Fbeen/RetroLink/src/USBHost.c

#include <string.h>
#include "CH559.h"
#include "USBHost.h"
#include "hid_mouse.h"
#include "config.h"
#include "console.h"
#include "led.h"

/* laatste HID report voor wizard */
uint8_t __xdata g_last_report[LEARN_MAX_REPORT];
uint8_t g_last_report_len = 0;

/* Your parsers live elsewhere; keep the same signature you used before */
extern void parseMouseData(uint8_t hub, vendor_product_id_t *vp, unsigned char __xdata *report);
extern void parseJoystickData(uint8_t *report);
extern void rm_init(void);
extern void rj_init(void);

/* remember if there is a USB device connected */
static uint8_t device_present = 0;
static controller_mode_t currentMode = CTRL_MODE_NONE;

/* ---------------- Setup requests ---------------- */

typedef const unsigned char __code *PUINT8C;

__code unsigned char GetDeviceDescriptorRequest[] =
{
    USB_REQ_TYP_IN, USB_GET_DESCRIPTOR,
    0x00, USB_DESCR_TYP_DEVICE,
    0x00, 0x00,
    sizeof(USB_DEV_DESCR), 0x00
};

__code unsigned char GetConfigurationDescriptorRequest[] =
{
    USB_REQ_TYP_IN, USB_GET_DESCRIPTOR,
    0x00, USB_DESCR_TYP_CONFIG,
    0x00, 0x00,
    /* first fetch only config header size */
    sizeof(USB_CFG_DESCR), 0x00
};

__code unsigned char SetUSBAddressRequest[] =
{
    USB_REQ_TYP_OUT, USB_SET_ADDRESS,
    USB_DEVICE_ADDR, 0x00,
    0x00, 0x00,
    0x00, 0x00
};

__code unsigned char SetupSetUsbConfig[] =
{
    USB_REQ_TYP_OUT, USB_SET_CONFIGURATION,
    0x00, 0x00,
    0x00, 0x00,
    0x00, 0x00
};

__code unsigned char SetHIDIdleRequest[] =
{
    USB_REQ_TYP_CLASS | USB_REQ_RECIP_INTERF, HID_SET_IDLE,
    0x00, 0x00,
    0x00, 0x00,
    0x00, 0x00
};

/* ---------------- Buffers ---------------- */

#ifndef MAX_PACKET_SIZE
#define MAX_PACKET_SIZE 64
#endif

__at(0x0000) unsigned char __xdata RxBuffer[MAX_PACKET_SIZE];
__at(0x0100) unsigned char __xdata TxBuffer[MAX_PACKET_SIZE];

#define RECEIVE_BUFFER_LEN 128
__xdata unsigned char receiveDataBuffer[RECEIVE_BUFFER_LEN];

/* ---------------- Minimal state ---------------- */

uint8_t endpoint0Size;

static root_hub_device_t __xdata rootHubDevice;
static hid_device_t __xdata hidDevice;
static vendor_product_id_t __xdata vendorProductID;

/* ---------------- Helpers ---------------- */

/*
 * Copy a setup/request packet from code memory to the TX buffer.
 */
static void fillTxBuffer(PUINT8C data, unsigned char len)
{
    unsigned char i;
    for (i = 0; i < len; i++)
        TxBuffer[i] = data[i];
}

/*
 * Set the current USB device address for host communication.
 */
static void setHostUsbAddr(unsigned char addr)
{
    USB_DEV_AD = (USB_DEV_AD & bUDA_GP_BIT) | (addr & 0x7F);
}

/*
 * Configure USB speed (full-speed or low-speed).
 */
static void setUsbSpeed(unsigned char fullSpeed)
{
    if (fullSpeed)
    {
        USB_CTRL &= ~bUC_LOW_SPEED;
        UH_SETUP &= ~bUH_PRE_PID_EN;
    }
    else
    {
        USB_CTRL |= bUC_LOW_SPEED;
    }
}

/*
 * Disable the root hub port and reset internal state.
 */
static void disableRootHubPort(void)
{
    rootHubDevice.status  = ROOT_DEVICE_DISCONNECT;
    rootHubDevice.address = 0;
    rootHubDevice.speed   = 1;

    UHUB0_CTRL = 0;
}

/*
 * Reset the root hub port and prepare for enumeration.
 */
static void resetRootHubPort(void)
{
    endpoint0Size = DEFAULT_ENDP0_SIZE;
    setHostUsbAddr(0);
    setUsbSpeed(1);

    UHUB0_CTRL = (UHUB0_CTRL & ~bUH_LOW_SPEED) | bUH_BUS_RESET;
    delay(15);
    UHUB0_CTRL = (UHUB0_CTRL & ~bUH_BUS_RESET);

    delayUs(250);
    UIF_DETECT = 0;
}

/*
 * Enable the root hub port if a device is attached.
 * Detects device speed and configures the controller accordingly.
 */
static unsigned char enableRootHubPort(void)
{
    if (USB_HUB_ST & bUHS_H0_ATTACH)
    {
        if ((UHUB0_CTRL & bUH_PORT_EN) == 0x00)
        {
            if (USB_HUB_ST & bUHS_DM_LEVEL)
            {
                rootHubDevice.speed = 0;
                UHUB0_CTRL |= bUH_LOW_SPEED;
            }
            else
            {
                rootHubDevice.speed = 1;
                UHUB0_CTRL &= ~bUH_LOW_SPEED;
            }
        }
        UHUB0_CTRL |= bUH_PORT_EN;
        return ERR_SUCCESS;
    }
    return ERR_USB_DISCON;
}

/*
 * Select the currently active USB device (address + speed).
 */
static void selectHubPort(void)
{
    setHostUsbAddr(rootHubDevice.address);
    setUsbSpeed(rootHubDevice.speed);
}

/* ---------------- USB transfers ---------------- */

/*
 * Perform a low-level USB host transfer (SETUP/IN/OUT).
 * Handles retries, NAKs and toggle bits.
 */
static unsigned char hostTransfer(unsigned char endp_pid, unsigned char tog, unsigned short timeout)
{
    static unsigned short retries = 0;
    static unsigned char  r;
    static unsigned short i;

    UH_RX_CTRL = tog;
    UH_TX_CTRL = tog;

    do
    {
        UH_EP_PID = endp_pid;
        UIF_TRANSFER = 0;

        for (i = 200; i != 0 && UIF_TRANSFER == 0; i--)
            delayUs(1);

        UH_EP_PID = 0x00;

        if (UIF_TRANSFER == 0)
            return ERR_USB_UNKNOWN;

        if (U_TOG_OK)
            return ERR_SUCCESS;

        r = USB_INT_ST & MASK_UIS_H_RES;

        if (r == USB_PID_STALL)
            return (r | ERR_USB_TRANSFER);

        if (r == USB_PID_NAK)
        {
            if (timeout == 0)
                return (r | ERR_USB_TRANSFER);
            if (timeout < 0xFFFF)
                timeout--;
            /* keep retrying */
        }
        else
        {
            /* For most cases, treat other responses as transfer error */
            if (r == USB_PID_ACK)
                return ERR_SUCCESS;

            if (r == USB_PID_DATA0 || r == USB_PID_DATA1)
                return ERR_SUCCESS;

            if (r)
                return (r | ERR_USB_TRANSFER);
        }

        delayUs(15);
    }
    while (++retries < 200);

    return ERR_USB_TRANSFER;
}

/*
 * Perform a USB control transfer (setup + optional data + status stage).
 * Used for enumeration and standard USB requests.
 */
static unsigned char hostCtrlTransfer(unsigned char __xdata *DataBuf, unsigned short *RetLen, unsigned short maxLength)
{
    static unsigned short RemLen;
    static unsigned char  s, RxLen, i;
    static unsigned char __xdata *pBuf;

    pBuf = DataBuf;

    PXUSB_SETUP_REQ pSetupReq = (PXUSB_SETUP_REQ)TxBuffer;

    delayUs(200);

    if (RetLen)
        *RetLen = 0;

    UH_TX_LEN = sizeof(USB_SETUP_REQ);
    s = hostTransfer((unsigned char)(USB_PID_SETUP << 4), 0, 10000);
    if (s != ERR_SUCCESS)
        return s;

    UH_RX_CTRL = UH_TX_CTRL = bUH_R_TOG | bUH_R_AUTO_TOG | bUH_T_TOG | bUH_T_AUTO_TOG;
    UH_TX_LEN = 0x01;

    RemLen = ((unsigned short)pSetupReq->wLengthH << 8) | pSetupReq->wLengthL;

    if (RemLen && pBuf)
    {
        if (pSetupReq->bRequestType & USB_REQ_TYP_IN)
        {
            while (RemLen)
            {
                s = hostTransfer((unsigned char)(USB_PID_IN << 4), UH_RX_CTRL, 10000);
                if (s != ERR_SUCCESS)
                    return s;

                RxLen = (USB_RX_LEN < RemLen) ? USB_RX_LEN : RemLen;
                RemLen -= RxLen;

                if (RetLen)
                    *RetLen += RxLen;

                for (i = 0; i < RxLen; i++)
                    pBuf[i] = RxBuffer[i];

                pBuf += RxLen;

                if (USB_RX_LEN == 0 || USB_RX_LEN < endpoint0Size)
                    break;
            }
            UH_TX_LEN = 0x00;
        }
        else
        {
            /* OUT data stage not used by our minimal stack (except rare class reqs),
               but keep structure intact. */
            while (RemLen)
            {
                UH_TX_LEN = (RemLen >= endpoint0Size) ? endpoint0Size : RemLen;
                s = hostTransfer((unsigned char)(USB_PID_OUT << 4), UH_TX_CTRL, 10000);
                if (s != ERR_SUCCESS)
                    return s;

                RemLen -= UH_TX_LEN;
                if (RetLen)
                    *RetLen += UH_TX_LEN;
            }
        }
    }

    s = hostTransfer((UH_TX_LEN ? (USB_PID_IN << 4) : (USB_PID_OUT << 4)),
                     bUH_R_TOG | bUH_T_TOG, 10000);
    if (s != ERR_SUCCESS)
        return s;

    if (UH_TX_LEN == 0 || USB_RX_LEN == 0)
        return ERR_SUCCESS;

    return ERR_USB_BUF_OVER;
}

/* ---------------- Enumeration steps ---------------- */

/*
 * Request and parse the USB device descriptor.
 * Extracts endpoint size and stores VID/PID.
 */
static unsigned char getDeviceDescriptor(void)
{
    unsigned char s;
    unsigned short len;

    endpoint0Size = DEFAULT_ENDP0_SIZE;

    fillTxBuffer(GetDeviceDescriptorRequest, sizeof(GetDeviceDescriptorRequest));
    s = hostCtrlTransfer(receiveDataBuffer, &len, RECEIVE_BUFFER_LEN);
    if (s != ERR_SUCCESS)
        return s;

    endpoint0Size = ((PXUSB_DEV_DESCR)receiveDataBuffer)->bMaxPacketSize0;

    /* Store VID/PID for your config table */
    vendorProductID.idVendorL  = ((PXUSB_DEV_DESCR)receiveDataBuffer)->idVendorL;
    vendorProductID.idVendorH  = ((PXUSB_DEV_DESCR)receiveDataBuffer)->idVendorH;
    vendorProductID.idProductL = ((PXUSB_DEV_DESCR)receiveDataBuffer)->idProductL;
    vendorProductID.idProductH = ((PXUSB_DEV_DESCR)receiveDataBuffer)->idProductH;

    return ERR_SUCCESS;
}

/*
 * Assign a USB address to the connected device.
 */
static unsigned char setUsbAddress(unsigned char addr)
{
    unsigned char s;
    PXUSB_SETUP_REQ pSetupReq = (PXUSB_SETUP_REQ)TxBuffer;

    fillTxBuffer(SetUSBAddressRequest, sizeof(SetUSBAddressRequest));
    pSetupReq->wValueL = addr;

    s = hostCtrlTransfer(0, 0, 0);
    if (s != ERR_SUCCESS)
        return s;

    setHostUsbAddr(addr);
    delay(100);

    return ERR_SUCCESS;
}

/*
 * Retrieve the full configuration descriptor from the device.
 */
static unsigned char getConfigurationDescriptor(void)
{
    unsigned char s;
    unsigned short len;
    unsigned short total;

    /* 1) fetch config header */
    fillTxBuffer(GetConfigurationDescriptorRequest, sizeof(GetConfigurationDescriptorRequest));
    s = hostCtrlTransfer(receiveDataBuffer, &len, RECEIVE_BUFFER_LEN);
    if (s != ERR_SUCCESS)
        return s;

    total = (unsigned short)((PXUSB_CFG_DESCR)receiveDataBuffer)->wTotalLengthL |
            ((unsigned short)((PXUSB_CFG_DESCR)receiveDataBuffer)->wTotalLengthH << 8);

    if (total > RECEIVE_BUFFER_LEN)
        return ERR_USB_BUF_OVER;

    /* 2) fetch full config */
    fillTxBuffer(GetConfigurationDescriptorRequest, sizeof(GetConfigurationDescriptorRequest));
    ((PXUSB_SETUP_REQ)TxBuffer)->wLengthL = (unsigned char)(total & 0xFF);
    ((PXUSB_SETUP_REQ)TxBuffer)->wLengthH = (unsigned char)(total >> 8);

    s = hostCtrlTransfer(receiveDataBuffer, &len, RECEIVE_BUFFER_LEN);
    if (s != ERR_SUCCESS)
        return s;

    return ERR_SUCCESS;
}

/*
 * Set the active USB configuration.
 */
static unsigned char setUsbConfig(unsigned char cfg)
{
    PXUSB_SETUP_REQ pSetupReq = (PXUSB_SETUP_REQ)TxBuffer;

    fillTxBuffer(SetupSetUsbConfig, sizeof(SetupSetUsbConfig));
    pSetupReq->wValueL = cfg;

    return hostCtrlTransfer(0, 0, 0);
}

/*
 * Send HID SetIdle request to reduce report rate (optional).
 */
static void setHidIdle(uint8_t interfaceNumber)
{
    /* Not fatal if this fails; many devices ignore it. */
    fillTxBuffer(SetHIDIdleRequest, sizeof(SetHIDIdleRequest));
    ((PXUSB_SETUP_REQ)TxBuffer)->wIndexL = interfaceNumber;
    (void)hostCtrlTransfer(0, 0, 0);
}

/*
 * Find and bind the first HID interface and its interrupt IN endpoint.
 */
static unsigned char bindFirstHidInterface(void)
{
    static unsigned short total;
    static unsigned short i;

    PXUSB_CFG_DESCR cfg = (PXUSB_CFG_DESCR)receiveDataBuffer;
    total = (unsigned short)cfg->wTotalLengthL | ((unsigned short)cfg->wTotalLengthH << 8);

    PXUSB_ITF_DESCR currentInterface = 0;

    hidDevice.connected = 0;
    hidDevice.type      = HID_TYPE_UNKNOWN;
    hidDevice.endpoint  = 0;
    hidDevice.interface = 0;
    hidDevice.toggle    = 0;

    i = cfg->bLength;

    while (i < total)
    {
        unsigned char __xdata *desc = &receiveDataBuffer[i];

        if (desc[0] == 0) /* safety */
            break;

        switch (desc[1])
        {
            case USB_DESCR_TYP_INTERF:
            {
                currentInterface = (PXUSB_ITF_DESCR)desc;

                if (currentInterface->bInterfaceClass == USB_DEV_CLASS_HID)
                {
                    /* Protocol: 2 = mouse, 1 = keyboard, 0 = none (joystick/gamepad often uses 0) */
                    if (currentInterface->bInterfaceProtocol == 2)
                        hidDevice.type = HID_TYPE_MOUSE;
                    else
                        hidDevice.type = HID_TYPE_JOYSTICK;

                    hidDevice.interface = currentInterface->bInterfaceNumber;
                }
                break;
            }

            case USB_DESCR_TYP_ENDP:
            {
                if (currentInterface && currentInterface->bInterfaceClass == USB_DEV_CLASS_HID)
                {
                    PXUSB_ENDP_DESCR ep = (PXUSB_ENDP_DESCR)desc;

                    /* We want Interrupt IN endpoint */
                    if ((ep->bEndpointAddress & 0x80) && ((ep->bmAttributes & 0x03) == 0x03))
                    {
                        hidDevice.endpoint  = ep->bEndpointAddress;
                        hidDevice.connected = 1;
                        hidDevice.toggle    = 0;

                        setHidIdle(hidDevice.interface);
                        return ERR_SUCCESS;
                    }
                }
                break;
            }

            default:
                break;
        }

        i += desc[0];
    }

    return ERR_USB_UNSUPPORT;
}

/* ---------------- Public API ---------------- */

/*
 * Reset all USB device-related state and clear stored VID/PID.
 */
void resetHubDevices(uint8_t hubindex)
{
    /* keep signature; only hubindex==0 exists */
    (void)hubindex;

    vendorProductID.idVendorL  = 0;
    vendorProductID.idVendorH  = 0;
    vendorProductID.idProductL = 0;
    vendorProductID.idProductH = 0;

    hidDevice.connected = 0;
    hidDevice.type      = HID_TYPE_UNKNOWN;
    hidDevice.endpoint  = 0;
    hidDevice.interface = 0;
    hidDevice.toggle    = 0;
}

/*
 * Initialize the CH559 USB host controller.
 */
void initUSB_Host(void)
{
    IE_USB = 0;

    USB_CTRL   = bUC_HOST_MODE;
    USB_DEV_AD = 0x00;

    UH_EP_MOD  = bUH_EP_TX_EN | bUH_EP_RX_EN;
    UH_RX_DMA  = 0x0000;
    UH_TX_DMA  = 0x0001;

    UH_RX_CTRL = 0x00;
    UH_TX_CTRL = 0x00;

    USB_CTRL   = bUC_HOST_MODE | bUC_INT_BUSY | bUC_DMA_EN;
    UH_SETUP   = bUH_SOF_EN;

    USB_INT_FG = 0xFF;

    disableRootHubPort();
    resetHubDevices(0);

    USB_INT_EN = bUIE_TRANSFER | bUIE_DETECT;

    setControllerMode(CTRL_MODE_NONE);

    initializeRootHubConnection();
}

/*
 * Perform full USB enumeration on the root hub device.
 * Includes descriptor reading, address assignment and HID binding.
 */
static unsigned char initializeRootHubConnection(void)
{
    static unsigned char s;
    static unsigned char cfg;
    static unsigned char addr;
    static unsigned char i;
    static unsigned char retry;

    for (retry = 0; retry < 5; retry++)
    {
        delay(50);

        resetHubDevices(0);
        resetRootHubPort();

        /* enable port */
        for (i = 0; i < 100; i++)
        {
            delay(1);
            if (enableRootHubPort() == ERR_SUCCESS)
                break;
        }

        if (i == 100)
        {
            disableRootHubPort();

            if(device_present)
            {
                setControllerMode(CTRL_MODE_NONE);
                device_present = 0;
            }

            continue;
        }

        selectHubPort();

        s = getDeviceDescriptor();
        if (s != ERR_SUCCESS)
            continue;

        DEBUG_OUT("USB device VID:%02X%02X PID:%02X%02X\r\n",
            vendorProductID.idVendorH,
            vendorProductID.idVendorL,
            vendorProductID.idProductH,
            vendorProductID.idProductL);

        addr = 1;
        s = setUsbAddress(addr);
        if (s != ERR_SUCCESS)
            continue;

        rootHubDevice.address = addr;

        s = getConfigurationDescriptor();
        if (s != ERR_SUCCESS)
            continue;

        cfg = ((PXUSB_CFG_DESCR)receiveDataBuffer)->bConfigurationValue;

        s = setUsbConfig(cfg);
        if (s != ERR_SUCCESS)
            continue;

        s = bindFirstHidInterface();

        if (s == ERR_SUCCESS)
        {
            if(hidDevice.type == HID_TYPE_MOUSE)
            {
                setControllerMode(CTRL_MODE_MOUSE);
            }
            else
            {
                /* treat all other HID devices as joystick */
                setControllerMode(CTRL_MODE_JOYSTICK);
            }
        }
        else
        {
            /* device present but not usable for RetroLink */
            setControllerMode(CTRL_MODE_NONE);
        }

        rootHubDevice.status = ROOT_DEVICE_SUCCESS;
        return ERR_SUCCESS;
    }

    if(device_present)
    {
        puts("No device connected");
        device_present = 0;
    }

    rootHubDevice.status = ROOT_DEVICE_FAILED;
    return ERR_USB_UNKNOWN;
}

/*
 * Check for USB connect/disconnect events on the root hub.
 */
uint8_t checkRootHubConnections(void)
{
    unsigned char s = ERR_SUCCESS;

    if (!UIF_DETECT)
        return ERR_SUCCESS;

    UIF_DETECT = 0;

    if (USB_HUB_ST & bUHS_H0_ATTACH)
    {
        if (rootHubDevice.status == ROOT_DEVICE_DISCONNECT || (UHUB0_CTRL & bUH_PORT_EN) == 0x00)
        {
            disableRootHubPort();
            rootHubDevice.status = ROOT_DEVICE_CONNECTED;
            s = initializeRootHubConnection();
        }
    }
    else
    {
        if (rootHubDevice.status >= ROOT_DEVICE_CONNECTED)
        {
            resetHubDevices(0);
            disableRootHubPort();
            setControllerMode(CTRL_MODE_NONE);
            s = ERR_USB_DISCON;
        }
    }

    return s;
}

/*
 * Poll the connected HID device and process incoming reports.
 */
void pollHIDdevice(void)
{
    unsigned char s;
    unsigned char len;

    if (!hidDevice.connected)
        return;

    selectHubPort();

    s = hostTransfer(
            (USB_PID_IN << 4) | (hidDevice.endpoint & 0x7F),
            hidDevice.toggle ? (bUH_R_TOG | bUH_T_TOG) : 0,
            0);

    if (s != ERR_SUCCESS)
        return;

    hidDevice.toggle ^= 1;

    len = USB_RX_LEN;
    if (!len)
        return;

    /* kopieer report voor wizard */
    if(len > LEARN_MAX_REPORT)
        len = LEARN_MAX_REPORT;

    for(uint8_t i = 0; i < len; i++)
        g_last_report[i] = RxBuffer[i];

    g_last_report_len = len;
/*
puts("len=");
print_u8(g_last_report_len);
puts("\r\n");
    debug_print_report(g_last_report, g_last_report_len);
*/
    if (hidDevice.type == HID_TYPE_MOUSE)
    {
        hid_mouse_parse(RxBuffer);
    }
    else if (hidDevice.type == HID_TYPE_JOYSTICK)
    {
        parseJoystickData(g_last_report);
    }
}

/*
 * Set the active controller mode (mouse / joystick / none).
 * Initializes corresponding subsystem and triggers feedback.
 */
static void setControllerMode(controller_mode_t mode)
{
    if(mode == currentMode)
        return;

    currentMode = mode;

    switch(mode)
    {
        case CTRL_MODE_MOUSE:
            rm_init();
            puts("Mouse connected");
            led_activate(2000, 2000);
            break;

        case CTRL_MODE_JOYSTICK:
            rj_init();
            if(g_config.vid == get_vid() && g_config.pid == get_pid())
            {
                puts("Joystick connected");
                led_activate(2000, 2000);
            } else {
                start_learning(true);
            }
            break;

        case CTRL_MODE_NONE:
        default:
            puts("No controller");
            break;
    }
}

/*
 * Get the current controller mode.
 */
controller_mode_t USBHost_getControllerMode(void)
{
    return currentMode;
}

/*
 * Return the USB Vendor ID as a 16-bit value.
 */
uint16_t get_vid(void)
{
    return ((uint16_t)vendorProductID.idVendorH << 8) |
            vendorProductID.idVendorL;
}

/*
 * Return the USB Product ID as a 16-bit value.
 */
uint16_t get_pid(void)
{
    return ((uint16_t)vendorProductID.idProductH << 8) |
            vendorProductID.idProductL;
}
